robzach/Amelia/earlier_development/examples and tests/simple_tx_with_ranger_data/simple_tx_with_ranger_data.ino

// SimpleTx - the master or the transmitter

#include <SPI.h>
#include <nRF24L01.h>
#include <RF24.h>

#include <Wire.h>
#include <VL53L0X.h>

#define CE_PIN   7
#define CSN_PIN 8

const byte slaveAddress[5] = {'R', 'x', 'A', 'A', 'A'};


RF24 radio(CE_PIN, CSN_PIN); // Create a Radio
VL53L0X sensor;


int dataToSend = -10;
char txNum = '0';


unsigned long currentMillis;
unsigned long prevMillis;
unsigned long txIntervalMillis = 100;


void setup() {

  Serial.begin(9600);

  Serial.println("SimpleTx Starting");

  radio.begin();
  radio.setDataRate( RF24_250KBPS );
  radio.setRetries(3, 5); // delay, count
  radio.openWritingPipe(slaveAddress);

  Wire.begin();
  sensor.init();
  sensor.setTimeout(500);
}

//====================

void loop() {
  currentMillis = millis();
  if (currentMillis - prevMillis >= txIntervalMillis) {
    send();
    prevMillis = millis();
  }
}

//====================

void send() {

  bool rslt;
  rslt = radio.write( &dataToSend, sizeof(dataToSend) );
  // Always use sizeof() as it gives the size as the number of bytes.
  // For example if dataToSend was an int sizeof() would correctly return 2

  Serial.print("Data Sent ");
  Serial.print(dataToSend);
  if (rslt) {
    Serial.println("  Acknowledge received");
    updateMessage();
  }
  else {
    Serial.println("  Tx failed");
  }
}

//================

void updateMessage() {
  dataToSend = sensor.readRangeSingleMillimeters();
}
